Hardi-St/MobaLedLib_Turntable/src/Turntable/Dprintf.h

/*
 MobaLedLib: LED library for model railways
 ~~~~~~~~~~~~~~~~~~~~~~~~~~~~~~~~~~~~~~~~~~

 Copyright (C) 2018 - 2020  Hardi Stengelin: MobaLedLib@gmx.de

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
 You should have received a copy of the GNU Lesser General Public
 License along with this library; if not, write to the Free Software
 Foundation, Inc., 51 Franklin Street, Fifth Floor, Boston, MA  02110-1301 USA
 -------------------------------------------------------------------------------------------------------------

 Dprintf.h
 ~~~~~~~~~

 This module contains functions for formated printing with printf()

*/
#ifndef _Dprintf_h_
#define _Dprintf_h_

#if ENABLE_DPRINTF
// F() makro saves dynamic memory
   #define Dprintf(Format, ...) Dprintf_proc(F(Format), ##__VA_ARGS__)   // see: https://gcc.gnu.org/onlinedocs/cpp/Variadic-Macros.html
   #define Dprint2(txt, arg)    {Serial.print(F(txt)); Serial.print(arg);}
   #define Dprintln2(txt, arg)  {Serial.print(F(txt)); Serial.println(arg);}
   #define DprintT(txt)         Serial.print(F(txt))
   #define DprintA(arg, ...)    Serial.print(arg, ##__VA_ARGS__)
   #define DprintlnT(txt)       Serial.println(F(txt))
   #define DprintlnA(arg, ...)  Serial.println(arg, ##__VA_ARGS__)
#else
   #define Dprintf(Format, ...) {}
   #define Dprint2(txt, arg)    {}
   #define Dprintln2(txt, arg)  {}
   #define DprintT(txt)         {}
   #define DprintA(arg, ...)    {}
   #define DprintlnT(txt)       {}
   #define DprintlnA(arg, ...)  {}
#endif

#include <stdarg.h>
#include <WString.h>


//------------------------------------------------------
void Dprintf_proc(const __FlashStringHelper *format, ...)
//------------------------------------------------------
{
  char buf[50];
  va_list ap;
  va_start(ap, format);
  #ifdef __AVR__
     vsnprintf_P(buf, sizeof(buf), (const char *)format, ap); // progmem for AVR
  #else
     vsnprintf  (buf, sizeof(buf), (const char *)format, ap); // for the rest of the world
  #endif

  va_end(ap);
  Serial.print(buf);
}

#endif // _Printf_h_
